stccff/zelda_guardian_robot/model/bottom.SLDPRT

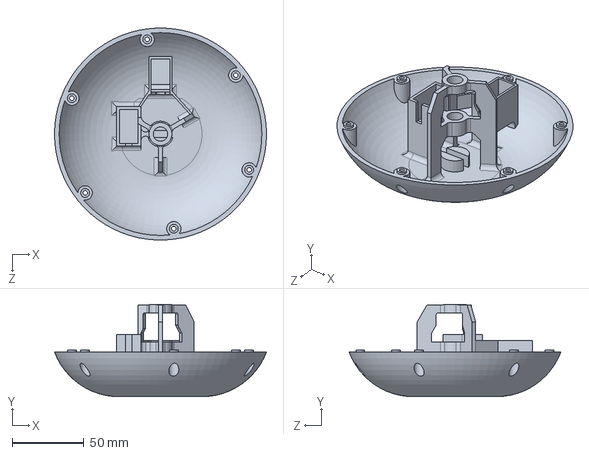
[picture p18: CAD file, 2024-05-19]
model/bottom.SLDPRT
147.3 x 64.2 x 147.3 mm
