stccff/zelda_guardian_robot/model/foot.SLDPRT

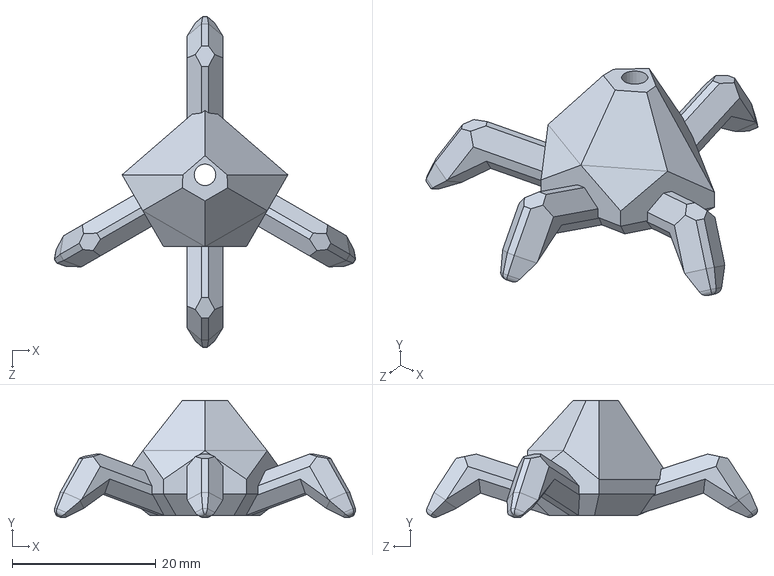
[picture p19: CAD file, 2024-05-19]
model/foot.SLDPRT
41.9 x 16.3 x 46.1 mm
