stccff/zelda_guardian_robot/model/oled_transparent.SLDPRT

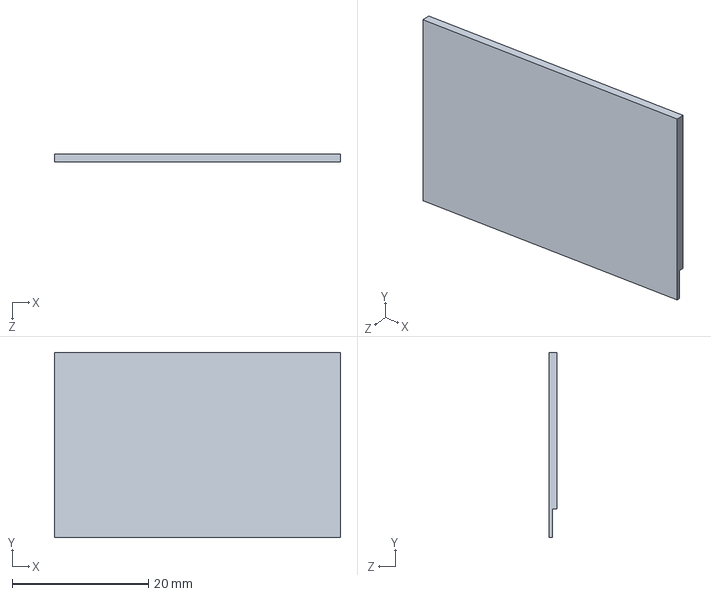
[picture p20: CAD file, 2024-05-19]
model/oled_transparent.SLDPRT
42.0 x 27.2 x 1.23 mm
