stccff/zelda_guardian_robot/model/decorative_gear.SLDPRT

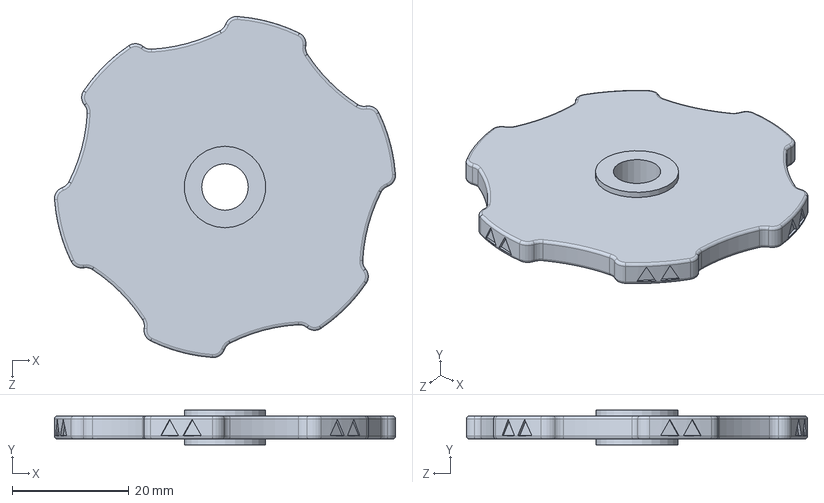
[picture p21: CAD file, 2024-05-19]
model/decorative_gear.SLDPRT
58.5 x 6.00 x 58.5 mm
