stccff/zelda_guardian_robot/model/speaker.SLDPRT

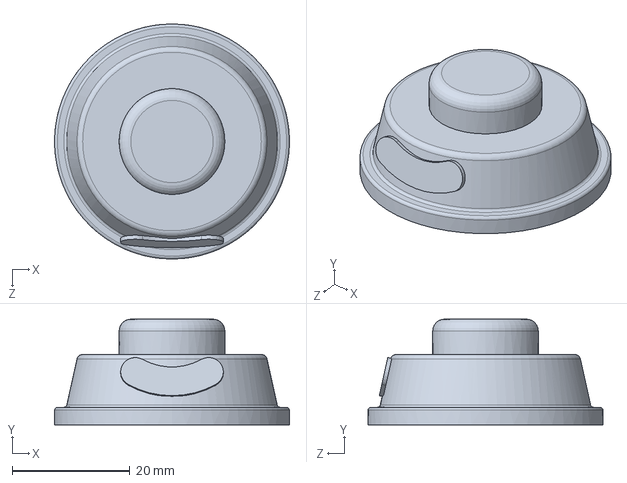
[picture p22: CAD file, 2024-05-19]
model/speaker.SLDPRT
40.0 x 18.0 x 40.0 mm
