stccff/zelda_guardian_robot/model/servo_motor(SG90).SLDPRT

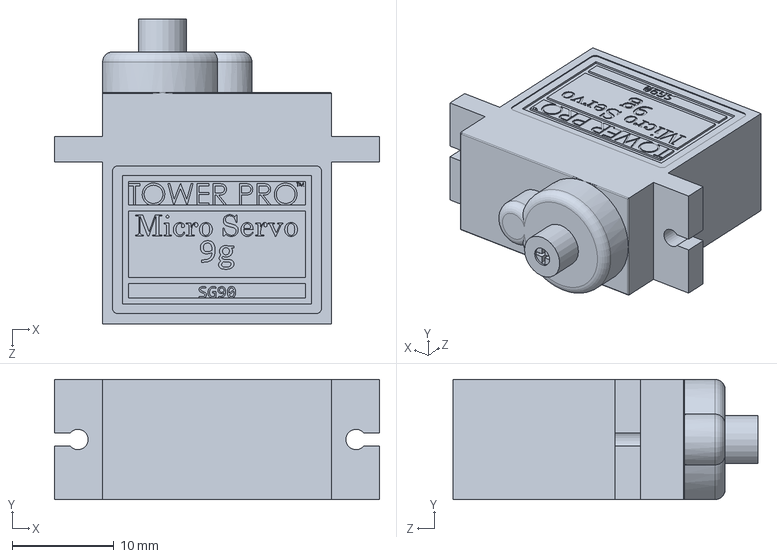
[picture p23: CAD file, 2024-05-19]
model/servo_motor(SG90).SLDPRT
31.9 x 11.8 x 29.9 mm
