stccff/zelda_guardian_robot/model/servo_motor_holder2.SLDPRT

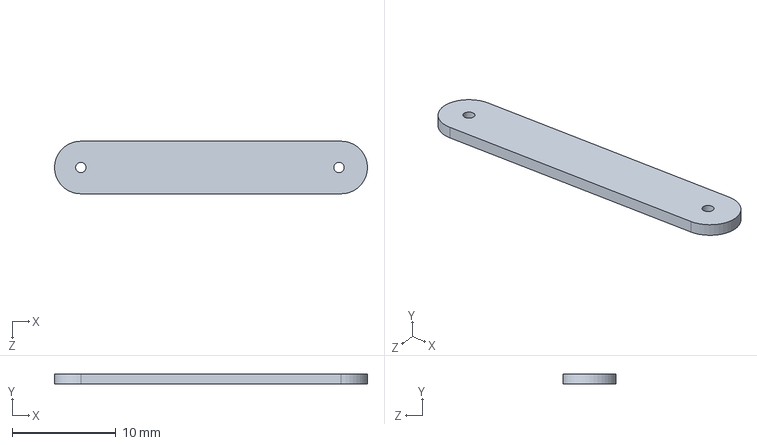
[picture p24: CAD file, 2024-05-19]
model/servo_motor_holder2.SLDPRT
30.2 x 1.00 x 5.08 mm
