stccff/zelda_guardian_robot/model/spur_gear_22x1_12.SLDPRT

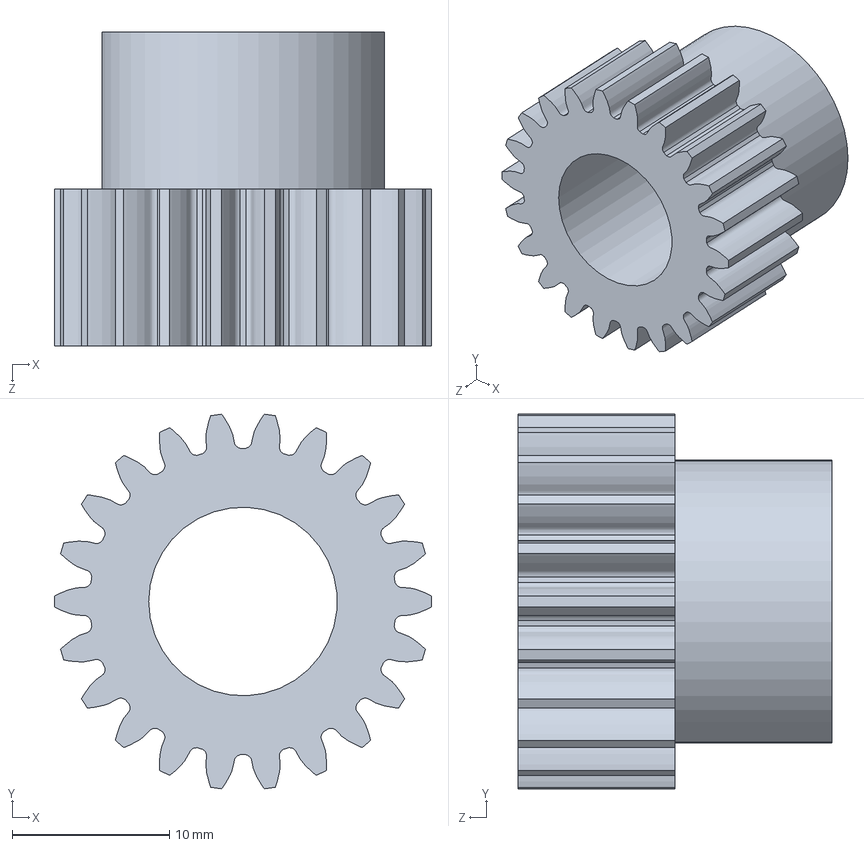
[picture p26: CAD file, 2024-05-19]
model/spur_gear_22x1_12.SLDPRT
24.0 x 23.8 x 20.0 mm
