stccff/zelda_guardian_robot/model/bevel_gear_25x1x6.SLDPRT

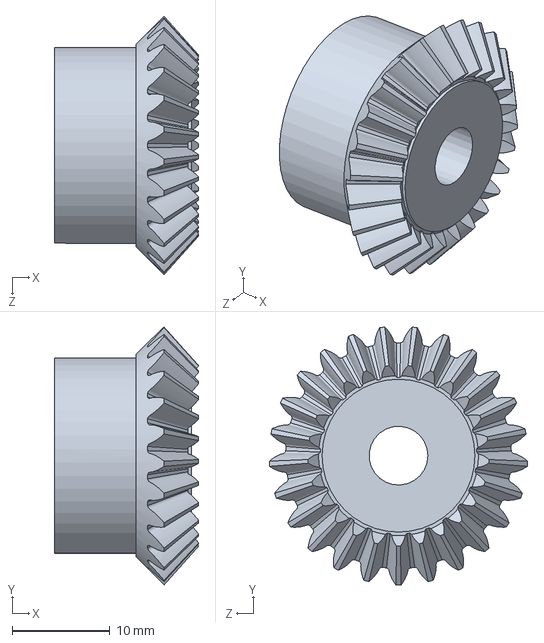
[picture p27: CAD file, 2024-05-19]
model/bevel_gear_25x1x6.SLDPRT
14.7 x 26.3 x 26.4 mm
