stccff/zelda_guardian_robot/model/head_connector.SLDPRT

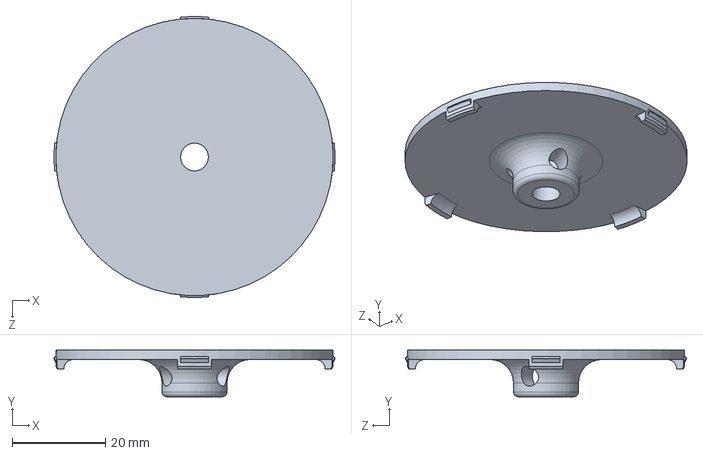
[picture p28: CAD file, 2024-05-19]
model/head_connector.SLDPRT
60.4 x 10.0 x 60.4 mm
