stccff/zelda_guardian_robot/model/mini_handle.SLDPRT

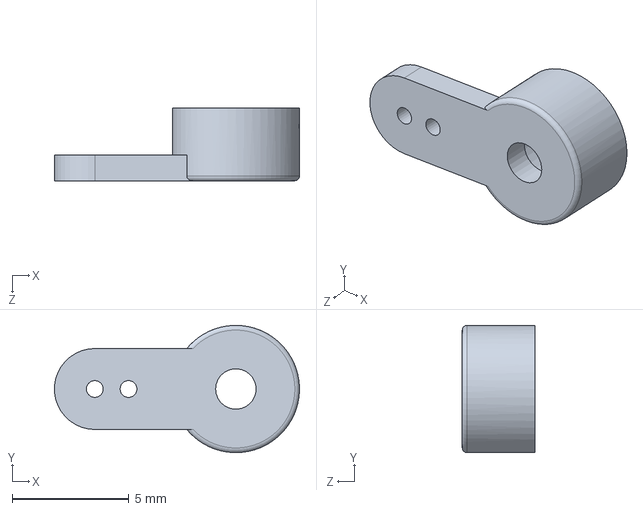
[picture p29: CAD file, 2024-05-19]
model/mini_handle.SLDPRT
10.5 x 5.44 x 3.10 mm
