stccff/zelda_guardian_robot/code/main/oled/picture.h

#ifndef __PICTURE_H
#define __PICTURE_H 
const unsigned char LOGO[] =
{
	0x00,0x00,0x00,0x00,0x00,0x00,0x00,0x00,0x00,0x00,0x00,0x00,0x00,0x00,0x00,0x00,
	0x00,0x00,0x00,0x00,0x00,0x00,0x00,0x00,0x00,0x00,0x00,0x80,0x80,0xC0,0xC0,0x80,
	0x00,0x00,0x00,0x00,0x00,0x00,0x00,0x00,0x00,0x00,0x00,0x00,0x00,0x00,0x00,0x00,
	0x00,0x00,0x00,0x00,0x00,0x00,0x00,0x00,0x00,0x00,0x00,0x00,0x00,0x00,0x00,0x00,
	0x00,0x00,0x00,0x00,0x00,0x00,0x00,0x00,0x00,0x60,0xE0,0xE0,0xF0,0xF0,0xF0,0xF0,
	0xF8,0xF8,0xF8,0xFC,0xFC,0xFE,0xFE,0xFE,0xFF,0xFF,0xFF,0xFF,0xFF,0xFF,0xFF,0xFF,
	0x00,0x00,0x00,0x00,0x00,0x80,0x80,0x80,0x80,0x00,0x00,0x00,0x00,0x00,0x00,0x00,
	0x00,0x00,0x00,0x00,0x00,0x00,0x00,0x00,0x00,0x00,0x00,0x00,0x00,0x00,0x00,0x00,
	0x00,0x00,0x00,0x00,0x00,0x00,0x00,0x00,0x00,0x00,0x00,0x01,0x01,0x03,0x07,0x0F,
	0x1F,0xBF,0x9F,0xDF,0xDF,0xEF,0x6F,0x67,0x77,0x33,0x3B,0x19,0x19,0x1D,0x0C,0x0E,
	0x0E,0x06,0x07,0x03,0x03,0x01,0x01,0x00,0x00,0x00,0x00,0x00,0x00,0x00,0x00,0x00,
	0x00,0x00,0x00,0x00,0x00,0x00,0x00,0x00,0x00,0x00,0x00,0x00,0x00,0x00,0x00,0x00,
	0x00,0x00,0x00,0x00,0x00,0x00,0x00,0x00,0x00,0x00,0x00,0x04,0x04,0x02,0x02,0x03,
	0x01,0x01,0xE1,0x18,0x04,0x00,0x02,0x02,0x02,0x02,0x02,0x04,0x08,0x30,0xC0,0x00,
	0x00,0x00,0x00,0xE0,0x18,0x0C,0x04,0x02,0x02,0x02,0x02,0x02,0x04,0x0C,0x18,0xE0,
	0x00,0x00,0x00,0x00,0x00,0x00,0x00,0x00,0x00,0x00,0x00,0x00,0x00,0x00,0x00,0x00,
	0x00,0x00,0x00,0x00,0x00,0x00,0x00,0x00,0x00,0x00,0x00,0x00,0x00,0x00,0x00,0x00,
	0x00,0x00,0x07,0x18,0x30,0x20,0x40,0x40,0x40,0x40,0x0E,0x2E,0x90,0x8C,0x83,0x83,
	0x83,0x83,0x83,0x87,0x88,0x90,0x26,0x46,0x46,0x40,0x40,0x40,0x20,0x10,0x08,0x07,
	0x00,0x00,0x00,0x00,0x00,0x00,0x00,0x00,0x00,0x00,0x00,0x00,0x00,0x00,0x00,0x00,
	0x00,0x00,0x00,0x00,0x00,0x00,0x00,0x00,0x00,0x00,0x00,0x00,0x00,0x00,0x00,0x00,
	0x00,0x00,0x00,0x00,0x00,0x00,0x80,0xE0,0xF8,0xFC,0xFE,0xFF,0xFF,0xFF,0x7F,0x1F,
	0x0F,0x0F,0x1F,0x7F,0xFF,0xFF,0xFF,0xFE,0xFC,0xF8,0xE0,0x80,0x00,0x00,0x00,0x00,
	0x00,0x00,0x00,0x00,0x00,0x00,0x00,0x00,0x00,0x00,0x00,0x00,0x00,0x00,0x00,0x00,
	0x00,0x00,0x00,0x00,0x00,0x00,0x00,0x00,0x00,0x00,0x00,0x00,0x00,0x00,0x00,0x00,
	0x00,0x60,0x60,0x70,0x3C,0x3F,0x3F,0x1F,0x1F,0x0F,0x07,0x03,0x01,0x00,0x00,0x00,
	0x00,0x00,0x00,0x00,0x00,0x01,0x07,0x0F,0x1F,0x1F,0x3F,0x7F,0x7C,0xF0,0xE0,0xC0,
	0x80,0x00,0x00,0x00,0x00,0x00,0x00,0x00,0x00,0x00,0x00,0x00,0x00,0x00,0x00,0x00,
	0x00,0x00,0x00,0x00,0x00,0x00,0x00,0x00,0x00,0x00,0x00,0x00,0x00,0x00,0x00,0x00,
	0x00,0x00,0x00,0x00,0x00,0x00,0x00,0x00,0x00,0x00,0x00,0x00,0x00,0x00,0x00,0x00,
	0x00,0x00,0x00,0x00,0x00,0x00,0x00,0x00,0x00,0x00,0x00,0x00,0x00,0x00,0x00,0x00,
	0x00,0x00,0x00,0x00,0x00,0x00,0x00,0x00,0x00,0x00,0x00,0x00,0x00,0x00,0x00,0x00
};

#endif
